sp5tof/APRS-Tracker-ArduinoProMini-with-NEO8M/Arduin_Pro_Mini/LibAPRS-master/device.h

#include "constants.h"

#ifndef DEVICE_CONFIGURATION
#define DEVICE_CONFIGURATION

// CPU settings
#ifndef TARGET_CPU
    #define TARGET_CPU m328p
#endif

#ifndef F_CPU
    #define F_CPU 16000000
#endif

#ifndef FREQUENCY_CORRECTION
    #define FREQUENCY_CORRECTION 0
#endif

// Sampling & timer setup
#define CONFIG_AFSK_DAC_SAMPLERATE 9600

// Port settings
#if TARGET_CPU == m328p
    #define DAC_PORT PORTD
    #define DAC_DDR  DDRD
    #define LED_PORT PORTB
    #define LED_DDR  DDRB

// Use Arduino digital pin 13 (PB5) for TX_PIN for Arduino Pro Mini and Arduino Nano
#if defined(ARDUINO_AVR_PRO) || defined(ARDUINO_AVR_NANO)
    #define LED_RX_PIN 0
    #define LED_TX_PIN 5
#else
    #define LED_RX_PIN 2
    #define LED_TX_PIN 1
#endif
    #define ADC_PORT PORTC
    #define ADC_DDR  DDRC
    #define ADC_PIN 0
    #define PPT_PIN 3
#endif

#endif
